drarosegrit-cpu/Rechenscheibe/output/previews/rotor_vorderseite_v3.png

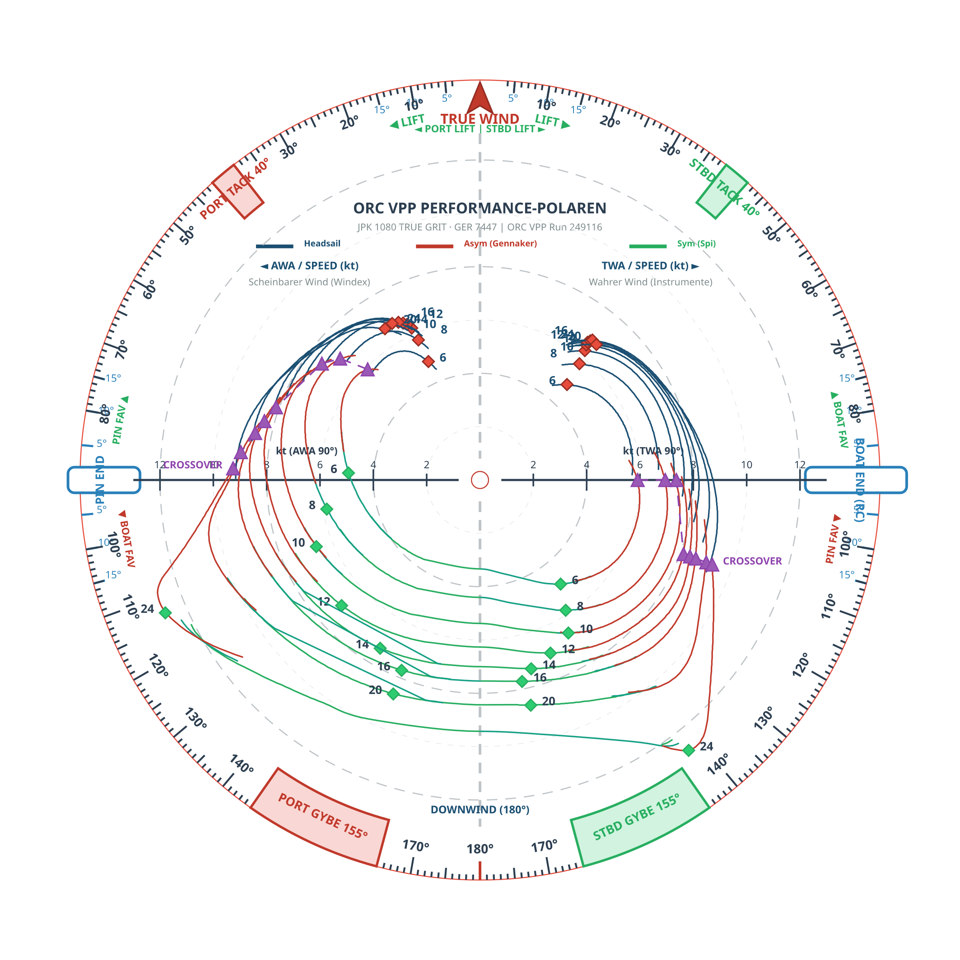
output/previews/rotor_vorderseite_v3.png
